2jaycollins/World-s-Worst-Alarm-Clock/src/animations.cpp

#include "animations.h"

// ============================================================================
//  ANIMATION FRAME DATA
//  Big PROGMEM blobs live HERE, in the .cpp -- never in the header. A const
//  array in a header gets its own private copy in every .cpp that includes it,
//  which silently duplicates it in flash with no warning. The header only
//  declares the Anim, which is 12 bytes.
//
//  ADDING AN ANIMATION
//    1. Export frames (Wokwi animator / image2cpp). Adafruit-style byte arrays
//       drop straight in -- u8g2.drawBitmap() uses the same MSB-first order.
//    2. Paste the unique frames as a [N][bytes] array below.
//    3. Add an order[] table if frames repeat (see the note on the eye).
//    4. Add one Anim definition + one extern line in animations.h.
//
//  COST: bytes-per-frame = (width/8) * height. 64x64 = 512B, 128x64 = 1024B,
//  32x32 = 128B. Crop hard and dedupe; flash is the tight resource here.
// ============================================================================

// ---- Eye blink (64x64) -----------------------------------------------------
// Auto-generated by https://wokwi.com/animator, graphics by icons8.com.
// The animator holds a pose by repeating whole frames, so the 27-step sequence
// only contains 14 distinct images. Storing the unique frames plus a 27-byte
// order table costs 7.2KB instead of 13.8KB for the same animation.
static const uint8_t EYE_FRAMES[14][512] PROGMEM = {
    { // frame 0
        0, 0, 0, 0, 0, 0, 0, 0, 0, 0, 0, 0, 0, 0, 0, 0, 0, 0, 0, 0, 0, 0, 0, 0,
        0, 0, 0, 0, 0, 0, 0, 0, 0, 0, 0, 0, 0, 0, 0, 0, 0, 0, 0, 0, 0, 0, 0, 0,
        0, 0, 0, 0, 0, 0, 0, 0, 0, 0, 0, 0, 0, 0, 0, 0, 0, 0, 0, 0, 0, 0, 0, 0,
        0, 0, 0, 0, 0, 0, 0, 0, 0, 0, 0, 0, 0, 0, 0, 0, 0, 0, 0, 0, 0, 0, 0, 0,
        0, 0, 0, 0, 0, 0, 0, 0, 0, 0, 0, 0, 0, 0, 0, 0, 0, 0, 0, 0, 0, 0, 0, 0,
        0, 0, 0, 31, 248, 0, 0, 0, 0, 0, 1, 255, 255, 128, 0, 0, 0, 0, 15, 255, 255, 240, 0, 0,
        0, 0, 63, 248, 31, 252, 0, 0, 0, 0, 255, 0, 0, 255, 0, 0, 0, 3, 252, 0, 0, 63, 192, 0,
        0, 7, 248, 0, 0, 31, 224, 0, 0, 31, 184, 7, 224, 29, 248, 0, 0, 62, 112, 15, 240, 14, 124, 0,
        0, 124, 112, 31, 248, 14, 62, 0, 1, 240, 96, 63, 252, 6, 15, 128, 3, 224, 96, 63, 252, 6, 7, 192,
        7, 192, 96, 63, 252, 6, 3, 224, 15, 0, 96, 63, 252, 6, 0, 240, 30, 0, 96, 63, 252, 6, 0, 120,
        60, 0, 96, 63, 252, 6, 0, 60, 120, 0, 112, 31, 248, 14, 0, 30, 120, 0, 112, 31, 248, 14, 0, 30,
        60, 0, 48, 7, 224, 12, 0, 60, 30, 0, 56, 0, 0, 28, 0, 120, 15, 0, 28, 0, 0, 56, 0, 240,
        7, 128, 28, 0, 0, 56, 1, 224, 3, 192, 14, 0, 0, 112, 3, 192, 0, 240, 7, 0, 0, 224, 15, 0,
        0, 120, 3, 192, 3, 192, 30, 0, 0, 62, 1, 248, 31, 128, 124, 0, 0, 15, 0, 127, 254, 0, 240, 0,
        0, 7, 192, 31, 248, 3, 224, 0, 0, 1, 240, 0, 0, 15, 128, 0, 0, 0, 126, 0, 0, 126, 0, 0,
        0, 0, 31, 192, 3, 248, 0, 0, 0, 0, 7, 255, 255, 224, 0, 0, 0, 0, 0, 255, 255, 0, 0, 0,
        0, 0, 0, 7, 224, 0, 0, 0, 0, 0, 0, 0, 0, 0, 0, 0, 0, 0, 0, 0, 0, 0, 0, 0,
        0, 0, 0, 0, 0, 0, 0, 0, 0, 0, 0, 0, 0, 0, 0, 0, 0, 0, 0, 0, 0, 0, 0, 0,
        0, 0, 0, 0, 0, 0, 0, 0, 0, 0, 0, 0, 0, 0, 0, 0, 0, 0, 0, 0, 0, 0, 0, 0,
        0, 0, 0, 0, 0, 0, 0, 0, 0, 0, 0, 0, 0, 0, 0, 0, 0, 0, 0, 0, 0, 0, 0, 0,
        0, 0, 0, 0, 0, 0, 0, 0, 0, 0, 0, 0, 0, 0, 0, 0, 0, 0, 0, 0, 0, 0, 0, 0,
        0, 0, 0, 0, 0, 0, 0, 0,
    },
    { // frame 1
        0, 0, 0, 0, 0, 0, 0, 0, 0, 0, 0, 0, 0, 0, 0, 0, 0, 0, 0, 0, 0, 0, 0, 0,
        0, 0, 0, 0, 0, 0, 0, 0, 0, 0, 0, 0, 0, 0, 0, 0, 0, 0, 0, 0, 0, 0, 0, 0,
        0, 0, 0, 0, 0, 0, 0, 0, 0, 0, 0, 0, 0, 0, 0, 0, 0, 0, 0, 0, 0, 0, 0, 0,
        0, 0, 0, 0, 0, 0, 0, 0, 0, 0, 0, 0, 0, 0, 0, 0, 0, 0, 0, 0, 0, 0, 0, 0,
        0, 0, 0, 0, 0, 0, 0, 0, 0, 0, 0, 0, 0, 0, 0, 0, 0, 0, 0, 0, 0, 0, 0, 0,
        0, 0, 0, 31, 248, 0, 0, 0, 0, 0, 1, 255, 255, 128, 0, 0, 0, 0, 15, 255, 255, 240, 0, 0,
        0, 0, 63, 255, 255, 252, 0, 0, 0, 0, 255, 255, 255, 255, 0, 0, 0, 3, 255, 252, 63, 255, 192, 0,
        0, 7, 254, 0, 0, 127, 224, 0, 0, 31, 248, 7, 224, 31, 248, 0, 0, 63, 240, 15, 240, 15, 252, 0,
        0, 127, 112, 31, 248, 14, 254, 0, 1, 252, 96, 63, 252, 6, 63, 128, 3, 240, 96, 63, 252, 6, 15, 192,
        7, 192, 96, 63, 252, 6, 7, 224, 15, 128, 96, 63, 252, 6, 1, 240, 30, 0, 96, 63, 252, 6, 0, 248,
        60, 0, 96, 63, 252, 6, 0, 60, 120, 0, 112, 31, 248, 14, 0, 30, 120, 0, 112, 31, 248, 14, 0, 30,
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
        1, 195, 192, 48, 224, 0, 0, 0, 1, 131, 128, 56, 224, 0, 0, 0, 1, 135,
        0, 56, 224, 0, 0, 0, 1, 206, 0, 61, 224, 0, 0, 0, 0, 254, 0, 31, 192,
        0, 0, 0, 0, 124, 0, 15, 128, 0, 0, 0, 0, 0, 0, 0, 0, 0, 0, 0, 0, 0, 0,
        0, 0, 0, 0, 0, 0, 0, 0, 0, 0, 0, 0,
    },
};

const Anim ANIM_WALK = {
    &WALK_FRAMES[0][0],  // frame data
    nullptr,             // no order table -- all 28 frames are unique
    64, 64,              // w, h
    28,                  // steps
    42                   // ms per step -> ~24fps, as the animator authored it
};
