2jaycollins/World-s-Worst-Alarm-Clock/include/secretsFILLER.h

// private stuff not for github
#ifndef SECRETS_H
#define SECRETS_H

#define H_WIFI_SSID "your_wifi_ssid"
#define H_WIFI_PASSWORD "your_wifi_password"

#define B_WIFI_SSID "your_other_wifi_ssid"
#define B_WIFI_PASSWORD "your_other_wifi_password"

#endif
